ntnunk/led_cube/PCB/controller.sch

## KiCad design PCB/controller.sch (2017-09-05)

Schematic: controller.sch

Parts:
C1: CP1
C2: 1000uF
C3, C7, C11: 10uF
C4, C8, C9, C10: 0.1uF
C5, C6: 22pF
D1: LED
D2, D3: 1N4001
J1: +12V_IN
J2: PWR_SW
J3: SERIAL
J4: PROG
J5: +5V_OUT
J6: DRV_SIG1
J7: DRV_SIG2
J8: LAYER_EN
Q1, Q2, Q3, Q4, Q5, Q6, Q7, Q8: 2N2222
R1, R4: 1K
R2, R3: 10k
R5, R6, R7, R8, R9, R10, R11, R12, R13: 330
SW1: DBG_SW
SW2: SW_Push
U1: ATMEGA328-PU; DIL28
U2: LM317T; TO-220
U3, U4: 74HC238
Y1: 16MHz
