ntnunk/led_cube/PCB/led_driver_board_1.sch

## KiCad design PCB/led_driver_board_1.sch (2017-09-05)

Schematic: led_driver_board_1.sch

Parts:
C12, C13, C15: 0.1uF
C14: 0.1uf
J9: SIG_IN
J10: LED_EN_OUT
J11: PWR_IN
R14, R15, R16, R17, R18, R19, R20, R21, R22, R23, R24, R25, R26, R27, R28, R29, R30, R31, R32, R33, R34, R35, R36, R37, R38, R39, R40, R41, R42, R43, R44, R45: 390
U5, U6, U7, U8: 74HC595
